gabethecabbage/vaillant_to_m30_trv_adaptor/vailant_nut.scad

include <openscad/polyScrewThread.scad>
include <valve_vars.scad>

hex_nut(outer_diameter+4,thread_length_circo*0.8,pitch,30,outer_diameter+1.5,0.5);
    
