gabethecabbage/vaillant_to_m30_trv_adaptor/valve_vars.scad

outer_diameter=38;
thread_length_circo=14;
thread_length_thermostat=7;

valve_diameter=29.9;
pitch=1.5;
thread_diameter=28.5;
pairing_start=2;
pairing_diameter=31;

pin_outer_diameter=5.8;
pin_inner_diameter=3.5;
pin_inner_height=4;
